dontworryboutit/AirQualitySensor/assets/IMG_1108.jpg

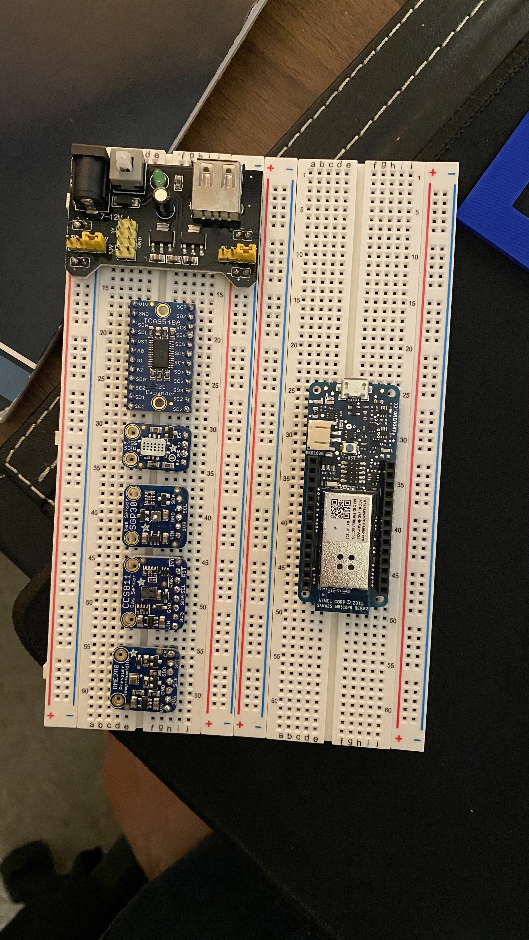
assets/IMG_1108.jpg
